polyramus/ev6-fittings/data/IMG_5350.jpeg

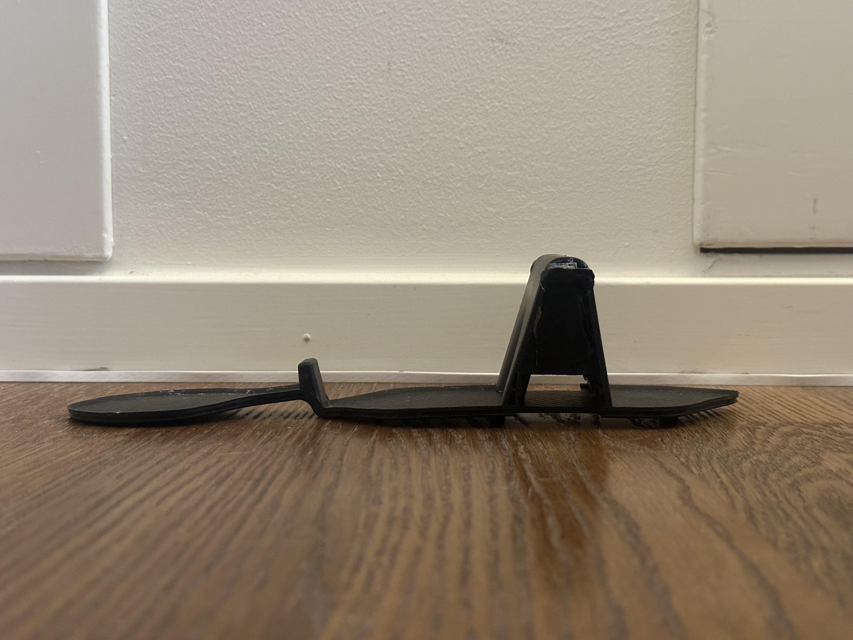
data/IMG_5350.jpeg
