polyramus/ev6-fittings/data/IMG_5344.jpg

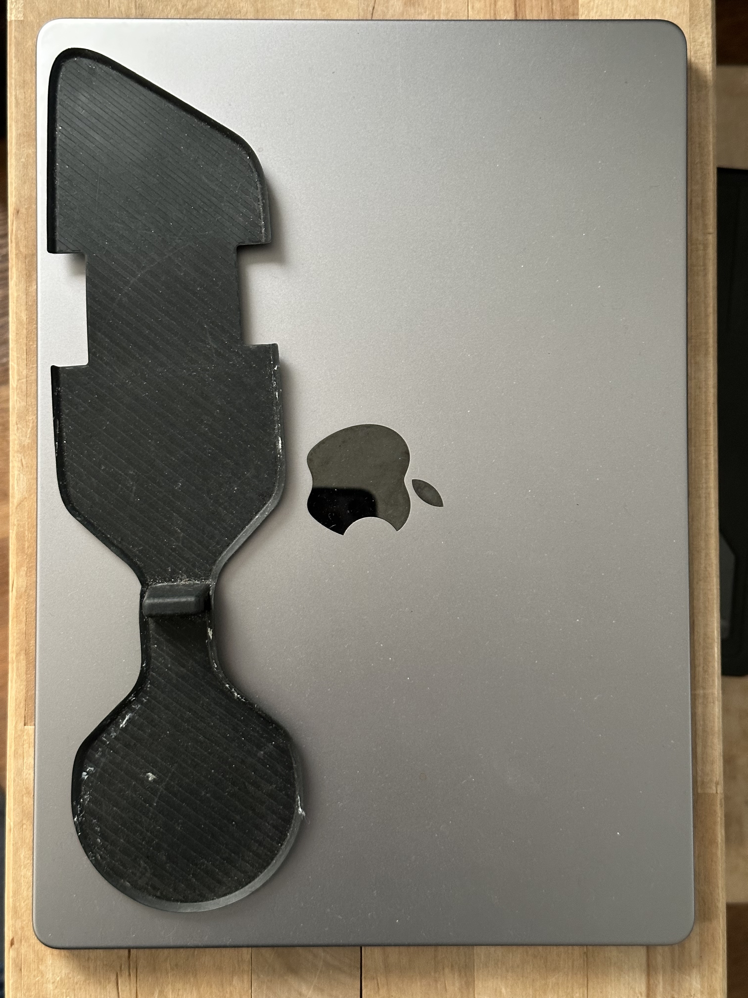
data/IMG_5344.jpg
