polyramus/ev6-fittings/data/IMG_5345.jpeg

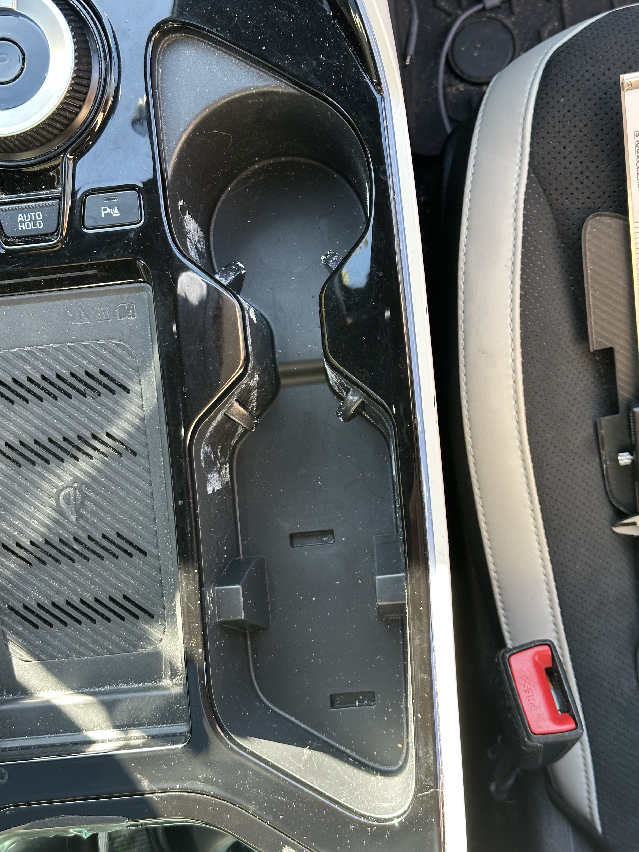
data/IMG_5345.jpeg
