polyramus/ev6-fittings/data/IMG_5348.jpeg

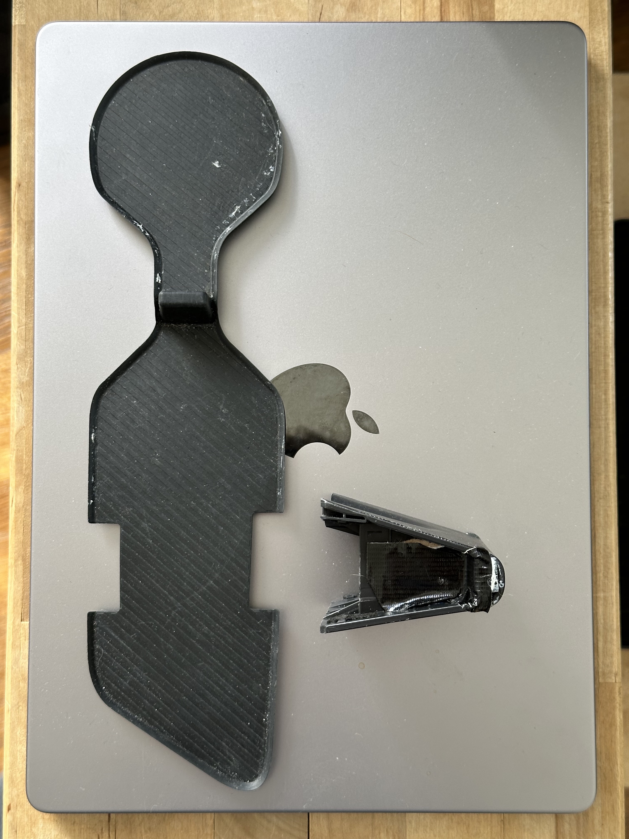
data/IMG_5348.jpeg
