polyramus/ev6-fittings/data/IMG_5349.jpeg

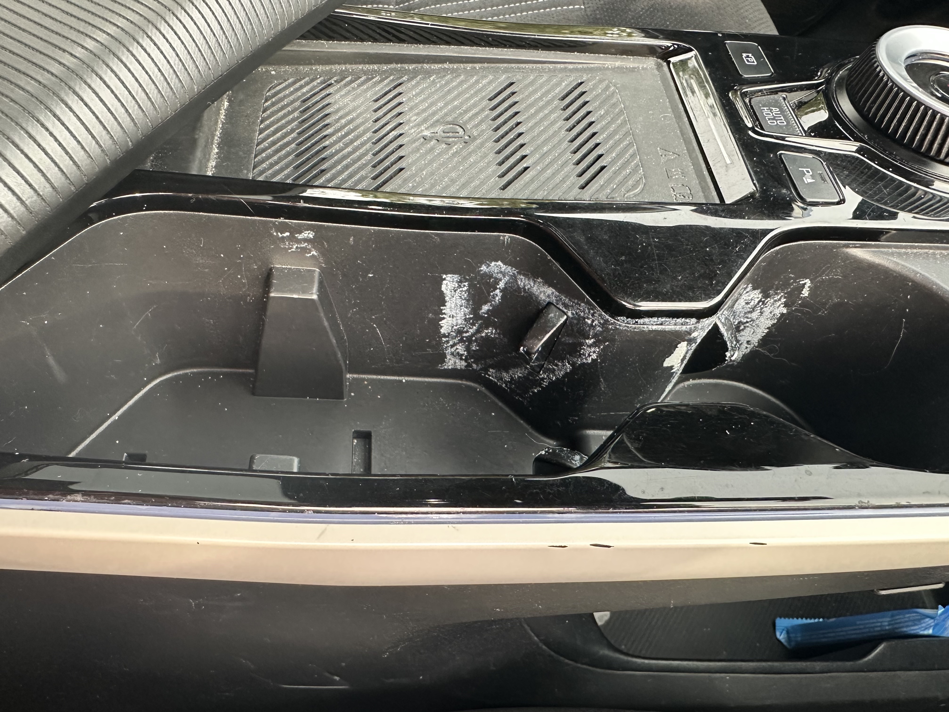
data/IMG_5349.jpeg
